azonenberg/latentred/rtl/engine/fabric/LineCardFIFOReader.sv

`timescale 1ns / 1ps
`default_nettype none
/***********************************************************************************************************************
*                                                                                                                      *
* LATENTRED                                                                                                            *
*                                                                                                                      *
* Copyright (c) 2012-2025 Andrew D. Zonenberg                                                                          *
* All rights reserved.                                                                                                 *
*                                                                                                                      *
* Redistribution and use in source and binary forms, with or without modification, are permitted provided that the     *
* following conditions are met:                                                                                        *
*                                                                                                                      *
*    * Redistributions of source code must retain the above copyright notice, this list of conditions, and the         *
*      following disclaimer.                                                                                           *
*                                                                                                                      *
*    * Redistributions in binary form must reproduce the above copyright notice, this list of conditions and the       *
*      following disclaimer in the documentation and/or other materials provided with the distribution.                *
*                                                                                                                      *
*    * Neither the name of the author nor the names of any contributors may be used to endorse or promote products     *
*      derived from this software without specific prior written permission.                                           *
*                                                                                                                      *
* THIS SOFTWARE IS PROVIDED BY THE AUTHORS "AS IS" AND ANY EXPRESS OR IMPLIED WARRANTIES, INCLUDING, BUT NOT LIMITED   *
* TO, THE IMPLIED WARRANTIES OF MERCHANTABILITY AND FITNESS FOR A PARTICULAR PURPOSE ARE DISCLAIMED. IN NO EVENT SHALL *
* THE AUTHORS BE HELD LIABLE FOR ANY DIRECT, INDIRECT, INCIDENTAL, SPECIAL, EXEMPLARY, OR CONSEQUENTIAL DAMAGES        *
* (INCLUDING, BUT NOT LIMITED TO, PROCUREMENT OF SUBSTITUTE GOODS OR SERVICES; LOSS OF USE, DATA, OR PROFITS; OR       *
* BUSINESS INTERRUPTION) HOWEVER CAUSED AND ON ANY THEORY OF LIABILITY, WHETHER IN CONTRACT, STRICT LIABILITY, OR TORT *
* (INCLUDING NEGLIGENCE OR OTHERWISE) ARISING IN ANY WAY OUT OF THE USE OF THIS SOFTWARE, EVEN IF ADVISED OF THE       *
* POSSIBILITY OF SUCH DAMAGE.                                                                                          *
*                                                                                                                      *
***********************************************************************************************************************/

/**
	@file
	@author Andrew D. Zonenberg
	@brief Read-side logic for the RX FIFO
 */

module LineCardFIFOReader #(

	//Global index of the first port in our line card
	parameter BASE_PORT			= 0,

	//Index of the crossbar port we're attached to
	parameter XBAR_PORT			= 0,

	parameter NUM_PORTS			= 50,
	localparam PORT_BITS		= $clog2(NUM_PORTS)

) (
	input wire					clk,

	//Read FIFO state
	input wire[12:0]			wr_ptr_committed[23:0],
	input wire					rd_ptr_reset[23:0],
	output logic[12:0]			rd_ptr[23:0],

	//URAM interface
	output logic				rd_en	= 0,
	output logic[16:0]			rd_addr	= 0,
	input wire[71:0]			rd_data,
	input wire					rd_valid,

	//Request/lookup interface to MAC address table
	AXIStream.transmitter		axi_lookup,
	AXIStream.receiver			axi_results,

	//AXI interface to core crossbar
	AXIStream.transmitter		axi_tx,
	input wire					xbar_ready
);

	////////////////////////////////////////////////////////////////////////////////////////////////////////////////////
	// Validate buses are the right size

	if(axi_tx.DATA_WIDTH != 64)
		axi_bus_width_inconsistent();

	////////////////////////////////////////////////////////////////////////////////////////////////////////////////////
	// Hook up AXI control signals

	assign axi_tx.aclk			= clk;
	assign axi_tx.twakeup		= 1;

	assign axi_lookup.aclk		= clk;
	assign axi_lookup.twakeup	= 1;

	assign axi_results.tready	= 1;

	initial begin
		axi_tx.areset_n		= 0;
		axi_tx.tvalid		= 0;
		axi_tx.tdata		= 0;
		axi_tx.tkeep		= 0;
		axi_tx.tstrb		= 0;
		axi_tx.tdest		= 0;
		axi_tx.tuser		= 0;
		axi_tx.tlast		= 0;

		axi_lookup.areset_n	= 0;
		axi_lookup.tvalid	= 0;
		axi_lookup.tdata	= 0;
		axi_lookup.tkeep	= 0;
		axi_lookup.tstrb	= 0;
		axi_lookup.tdest	= 0;
		axi_lookup.tuser	= 0;
		axi_lookup.tlast	= 0;
		axi_lookup.tid		= 0;
	end

	always_ff @(posedge clk) begin
		axi_tx.areset_n		<= 1;
		axi_lookup.areset_n	<= 1;
	end

	////////////////////////////////////////////////////////////////////////////////////////////////////////////////////
	// Stuff used to index state tables

	typedef enum logic[2:0]
	{
		//0 reserved for now
		MTYPE_HEADER	= 1,	//header read
		MTYPE_WORD0		= 2,
		MTYPE_WORD1		= 3,
		MTYPE_BODY		= 4,
		MTYPE_PREFETCH	= 5
	} mtype_t;

	//Round robin port counter
	logic[4:0]	main_rr_port	= 0;

	typedef struct packed
	{
		mtype_t		mtype;
		logic[4:0]	port;
	} PendingMetadata;

	PendingMetadata	meta_rdata;

	//Source of the packet currently being forwarded
	logic[4:0]		fwd_port	= 0;

	////////////////////////////////////////////////////////////////////////////////////////////////////////////////////
	// Per-port state tables

	typedef enum logic[3:0]
	{
		PORT_STATE_IDLE					= 0,	//nothing to do
		PORT_STATE_DATA_READY			= 1,	//frame ready to start forwarding
		PORT_STATE_HEADER				= 2,	//read of header was dispatched
		PORT_STATE_WORD_0				= 3,	//read of first payload word was dispatched
		PORT_STATE_WORD_1				= 4,	//read of second payload word was dispatched
		PORT_STATE_PREFETCH				= 5,	//prefetching more of the packet
		PORT_STATE_MAC_LOOKUP			= 6,	//mac address lookup in progress
		PORT_STATE_FWD_READY			= 7,	//ready to forward
		PORT_STATE_FORWARDING			= 8		//actively forwarding
	} PortState;

	//Current forwarding state
	PortState				port_states[23:0];

	//VLAN of the current frame
	vlan_t					port_vlans_replica0[23:0];
	vlan_t					port_vlans_replica1[23:0];

	//Dest MAC of the current frame
	macaddr_t				port_dst_mac_replica0[23:0];
	macaddr_t				port_dst_mac_replica1[23:0];

	//Source MAC of the current frame
	logic[15:0]				port_src_mac_hi_replica0[23:0];
	logic[15:0]				port_src_mac_hi_replica1[23:0];
	logic[31:0]				port_src_mac_lo_replica0[23:0];
	//logic[31:0]				port_src_mac_lo_replica1[23:0];

	//First 4 payload bytes of the current frame (ethertype and two more after)
	logic[31:0]				port_first4[23:0];

	//Length of the current frame
	logic[10:0]				port_lens[23:0];

	//Destination port of the current frame
	logic[PORT_BITS-1:0]	port_dst_port[23:0];
	logic					port_dst_is_broadcast[23:0];

	initial begin
		for(integer i=0; i<24; i++) begin
			port_states[i]				= PORT_STATE_IDLE;
			port_vlans_replica0[i]		= 0;
			port_vlans_replica1[i]		= 0;
			port_lens[i]				= 0;
			port_dst_mac_replica0[i]	= 0;
			port_dst_mac_replica1[i]	= 0;
			port_src_mac_hi_replica0[i]	= 0;
			port_src_mac_hi_replica1[i]	= 0;
			port_src_mac_lo_replica0[i]	= 0;
			//port_src_mac_lo_replica1[i]	= 0;
			port_first4[i]				= 0;
			port_dst_port[i]			= 0;
			port_dst_is_broadcast[i]	= 0;
			rd_ptr[i]					= 0;
		end
	end

	//Read side
	macaddr_t				port_dst_mac_metaport;
	macaddr_t				port_dst_mac_mainport;
	vlan_t					port_vlan_metaport;
	vlan_t					port_vlan_mainport;
	logic[10:0]				port_len_rdata;
	logic[15:0]				port_src_mac_hi_metaport;
	logic[15:0]				port_src_mac_hi_rrport;
	logic[31:0]				port_src_mac_lo_fwdport;
	always_comb begin
		port_dst_mac_metaport 		= port_dst_mac_replica0[meta_rdata.port];
		port_dst_mac_mainport 		= port_dst_mac_replica1[main_rr_port];

		port_vlan_metaport 			= port_vlans_replica0[meta_rdata.port];
		port_vlan_mainport 			= port_vlans_replica1[main_rr_port];

		port_len_rdata				= port_lens[main_rr_port];

		port_src_mac_hi_metaport	= port_src_mac_hi_replica0[meta_rdata.port];
		port_src_mac_lo_fwdport		= port_src_mac_lo_replica0[fwd_port];
		port_src_mac_hi_rrport		= port_src_mac_hi_replica1[main_rr_port];
	end

	//Write side
	logic		port_dst_mac_we;
	logic		port_vlan_we;
	logic		port_len_we;
	logic		port_src_mac_hi_we;
	logic		port_src_mac_lo_we;

	macaddr_t	port_dst_mac_wdata;
	vlan_t		port_vlan_wdata;
	logic[10:0]	port_len_wdata;
	logic[15:0]	port_src_mac_hi_wdata;
	logic[31:0]	port_src_mac_lo_wdata;

	always_comb begin
		port_vlan_we		= rd_valid && (meta_rdata.mtype == MTYPE_HEADER);
		port_len_we			= rd_valid && (meta_rdata.mtype == MTYPE_HEADER);
		port_dst_mac_we		= rd_valid && (meta_rdata.mtype == MTYPE_WORD0);
		port_src_mac_hi_we	= rd_valid && (meta_rdata.mtype == MTYPE_WORD0);
		port_src_mac_lo_we	= rd_valid && (meta_rdata.mtype == MTYPE_WORD1);

		port_dst_mac_wdata	=
		{
			rd_data[0*8 +: 8],
			rd_data[1*8 +: 8],
			rd_data[2*8 +: 8],
			rd_data[3*8 +: 8],
			rd_data[4*8 +: 8],
			rd_data[5*8 +: 8]
		};

		port_src_mac_hi_wdata =
		{
			rd_data[6*8 +: 8],
			rd_data[7*8 +: 8]
		};

		port_src_mac_lo_wdata =
		{
			rd_data[0*8 +: 8],
			rd_data[1*8 +: 8],
			rd_data[2*8 +: 8],
			rd_data[3*8 +: 8]
		};

		port_vlan_wdata		= rd_data[27:16];
		port_len_wdata		= rd_data[10:0];
	end
	always_ff @(posedge clk) begin
		if(port_dst_mac_we) begin
			port_dst_mac_replica0[meta_rdata.port]		<= port_dst_mac_wdata;
			port_dst_mac_replica1[meta_rdata.port]		<= port_dst_mac_wdata;
		end

		if(port_vlan_we) begin
			port_vlans_replica0[meta_rdata.port]		<= port_vlan_wdata;
			port_vlans_replica1[meta_rdata.port]		<= port_vlan_wdata;
		end

		if(port_len_we)
			port_lens[meta_rdata.port]					<= port_len_wdata;

		if(port_src_mac_hi_we) begin
			port_src_mac_hi_replica0[meta_rdata.port]	<= port_src_mac_hi_wdata;
			port_src_mac_hi_replica1[meta_rdata.port]	<= port_src_mac_hi_wdata;
		end

		if(port_src_mac_lo_we) begin
			port_src_mac_lo_replica0[meta_rdata.port]	<= port_src_mac_lo_wdata;
			//port_src_mac_lo_replica1[meta_rdata.port]	<= port_src_mac_lo_wdata;
		end

	end

	////////////////////////////////////////////////////////////////////////////////////////////////////////////////////
	// FIFO read helpers

	logic[12:0] fifo_rd_size[23:0];
	always_comb begin
		for(integer i=0; i<24; i=i+1)
			fifo_rd_size[i] = wr_ptr_committed[i] - rd_ptr[i];
	end

	////////////////////////////////////////////////////////////////////////////////////////////////////////////////////
	// State for in-progress packets

	PendingMetadata meta_wdata;

	wire			meta_empty;

	SingleClockFifo #(
		.WIDTH($bits(PendingMetadata)),
		.DEPTH(32),
		.USE_BLOCK(0),
		.OUT_REG(0)
	) meta_fifo (
		.clk(clk),

		.wr(rd_en),
		.din(meta_wdata),

		.rd(rd_valid),
		.dout(meta_rdata),

		.overflow(),
		.underflow(),
		.empty(meta_empty),
		.full(),
		.rsize(),
		.wsize(),
		.reset(!axi_tx.areset_n)
	);

	always_comb begin
		meta_wdata.port	= rd_addr[16:12];
	end

	////////////////////////////////////////////////////////////////////////////////////////////////////////////////////
	// Prefetch buffer

	//The actual memory
	logic[63:0] prefetch_buf[255:0];

	initial begin
		for(integer i=0; i<256; i++)
			prefetch_buf[i]	= 0;
	end

	//Prefetch progress for the current frame
	logic[2:0]		prefetch_wr_count		= 0;
	logic[2:0]		prefetch_wr_count_ff	= 0;
	logic[2:0]		prefetch_wr_count_ff2	= 0;
	logic[2:0]		prefetch_wr_count_ff3	= 0;
	logic[2:0]		prefetch_wr_count_ff4	= 0;
	logic[2:0]		prefetch_wr_count_ff5	= 0;
	logic[2:0]		prefetch_wr_count_ff6	= 0;

	logic			prefetch_wr_en;
	logic[7:0]		prefetch_wr_addr;
	logic[7:0]		prefetch_rd_addr		= 0;
	logic[63:0]		prefetch_rd_data;
	always_comb begin
		prefetch_wr_en		= rd_valid && (meta_rdata.mtype == MTYPE_PREFETCH);
		prefetch_wr_addr	= { meta_rdata.port, prefetch_wr_count_ff6 };
		prefetch_rd_data	= prefetch_buf[prefetch_rd_addr];
	end

	//Writes
	always_ff @(posedge clk) begin
		prefetch_wr_count_ff	<= prefetch_wr_count;
		prefetch_wr_count_ff2	<= prefetch_wr_count_ff;
		prefetch_wr_count_ff3	<= prefetch_wr_count_ff2;
		prefetch_wr_count_ff4	<= prefetch_wr_count_ff3;
		prefetch_wr_count_ff5	<= prefetch_wr_count_ff4;
		prefetch_wr_count_ff6	<= prefetch_wr_count_ff5;

		if(prefetch_wr_en)
			prefetch_buf[prefetch_wr_addr]	<= rd_data[63:0];
	end

	//Reads

	////////////////////////////////////////////////////////////////////////////////////////////////////////////////////
	// Main reader block

	//FIFO read pointer of the round robin winner
	logic[11:0]	main_rr_ptr;

	//FIFO read pointer of the most recent read transaction
	logic[11:0] meta_rdata_ptr;

	//FIFO read pointer of the frame being forwarded
	logic[11:0] fwd_ptr;

	always_comb begin
		main_rr_ptr		= rd_ptr[main_rr_port][11:0];
		meta_rdata_ptr	= rd_ptr[meta_rdata.port][11:0];
		fwd_ptr			= rd_ptr[fwd_port][11:0];
	end

	logic[10:0]	fwd_bytesToRead	= 0;
	logic[10:0]	fwd_bytesToSend	= 0;

	enum logic[2:0]
	{
		FWD_STATE_IDLE				= 0,
		FWD_STATE_HEADER_1			= 1,
		FWD_STATE_PREFETCH_DATA		= 2,
		FWD_STATE_BODY				= 3,
		FWD_STATE_TAIL				= 4
	} fwd_state = FWD_STATE_IDLE;

	//Figure out if we are available to begin forwarding a frame this cycle
	logic			canStartForwarding;
	always_comb begin

		canStartForwarding = 0;

		//Only proceed if previous frame isn't being actively forwarded
		if(fwd_state == FWD_STATE_IDLE)
			canStartForwarding = xbar_ready;

		//or it's ending this cycle
		if( (fwd_state == FWD_STATE_TAIL) && (fwd_bytesToSend <= 8) )
			canStartForwarding = xbar_ready;

	end

	//Combinatorially decide to increment read pointer
	logic[12:0]		rd_ptr_next[23:0];
	logic			rd_ptr_inc[23:0];
	always_comb begin

		//Default to not incrementing read pointer
		for(integer i=0; i<24; i++)
			rd_ptr_inc[i] = 0;

		//Actively forwarding?
		if( (fwd_state != FWD_STATE_IDLE) && (fwd_state != FWD_STATE_TAIL) ) begin

			case(fwd_state)
				FWD_STATE_HEADER_1:			rd_ptr_inc[fwd_port]	= 1;
				FWD_STATE_PREFETCH_DATA:	rd_ptr_inc[fwd_port]	= (fwd_bytesToRead > 0);
				FWD_STATE_BODY:				rd_ptr_inc[fwd_port]	= (fwd_bytesToRead > 0);
				default: begin
				end
			endcase

		end

		//Main port state machine
		else begin
			case(port_states[main_rr_port])
				PORT_STATE_DATA_READY:	rd_ptr_inc[main_rr_port]	= 1;
				PORT_STATE_HEADER:		rd_ptr_inc[main_rr_port]	= 1;
				PORT_STATE_WORD_0:		rd_ptr_inc[main_rr_port]	= 1;
				PORT_STATE_WORD_1:		rd_ptr_inc[main_rr_port]	= 1;
				PORT_STATE_FWD_READY: begin
					if( (port_len_rdata > 64) && canStartForwarding )
						rd_ptr_inc[main_rr_port]	= 1;
				end
				PORT_STATE_PREFETCH: begin
					if(prefetch_wr_count < 4)
						rd_ptr_inc[main_rr_port]	= 1;
				end

			endcase
		end

		//Calculate new read pointers
		for(integer i=0; i<24; i++) begin

			//Reset read pointer on request
			if(rd_ptr_reset[i])
				rd_ptr_next[i]		= 0;
			else if(rd_ptr_inc[i])
				rd_ptr_next[i]		= rd_ptr[i] + 1;
			else
				rd_ptr_next[i]		= rd_ptr[i];
		end

	end

	always_ff @(posedge clk) begin

		rd_en					<= 0;
		axi_lookup.tvalid		<= 0;
		axi_lookup.tlast		<= 0;

		//Clear AXI stuff on ack
		if(axi_tx.tready) begin
			axi_tx.tvalid		<= 0;
			axi_tx.tkeep		<= 0;
			axi_tx.tstrb		<= 0;
			axi_tx.tdata		<= 0;
			axi_tx.tlast		<= 0;
		end

		for(integer i=0; i<24; i++) begin

			//Register the calculated read pointer values
			//TODO: explicit replication for fanout control?
			rd_ptr[i]		<= rd_ptr_next[i];

			//Check all ports in parallel for having data ready to go
			if( (port_states[i] == PORT_STATE_IDLE) && (fifo_rd_size[i] != 0) )
				port_states[i]	<= PORT_STATE_DATA_READY;
		end

		//Handle MAC address lookups coming back
		if(axi_results.tvalid) begin
			port_dst_is_broadcast[axi_results.tid]	<= !axi_results.tuser[0];
			port_dst_port[axi_results.tid]			<= axi_results.tdata;
			port_states[axi_results.tid]			<= PORT_STATE_FWD_READY;

			`ifdef SIMULATION
				$display("[%t] Frame on interface %d is ready to forward",
					$realtime(),
					axi_results.tid + BASE_PORT);
			`endif
		end

		//Forwarding payload body
		if( (fwd_state == FWD_STATE_TAIL) || (fwd_state == FWD_STATE_BODY) ) begin

			//Full word?
			if(fwd_bytesToSend > 8) begin
				fwd_bytesToSend				<= fwd_bytesToSend - 8;
				axi_tx.tstrb				<= 8'hff;
			end

			//Partial word? We're done
			else begin
				case(fwd_bytesToSend)
					7:	axi_tx.tstrb		<= 8'b01111111;
					6:	axi_tx.tstrb		<= 8'b00111111;
					5:	axi_tx.tstrb		<= 8'b00011111;
					4:	axi_tx.tstrb		<= 8'b00001111;
					3:	axi_tx.tstrb		<= 8'b00000111;
					2:	axi_tx.tstrb		<= 8'b00000011;
					1:	axi_tx.tstrb		<= 8'b00000001;
					default: begin
						axi_tx.tstrb		<= 8'b00000000;
					end
				endcase

				axi_tx.tlast				<= 1;
				fwd_bytesToSend				<= 0;

				//Clear lots of state
				fwd_state					<= FWD_STATE_IDLE;
				port_states[fwd_port]		<= PORT_STATE_IDLE;

			end

			axi_tx.tvalid					<= 1;
			axi_tx.tdata					<= rd_data[63:0];
			axi_tx.tkeep					<= 8'hff;

		end

		//Request more data if we're fetching the body from URAM
		if(fwd_state == FWD_STATE_BODY) begin

			//Request more data unless we're done
			if(fwd_bytesToRead > 0) begin

				if(fwd_bytesToRead >= 8)
					fwd_bytesToRead				<= fwd_bytesToRead - 8;
				else
					fwd_bytesToRead				<= 0;

				//Request a read of the data
				rd_en							<= 1;
				rd_addr							<= { fwd_port, fwd_ptr };
				meta_wdata.mtype				<= MTYPE_BODY;

			end

			//Done reading? Move to tail unless this was a min-sized frame with no tail needed after prefetch
			else if(fwd_bytesToSend > 8)
				fwd_state						<= FWD_STATE_TAIL;

		end

		//Prefetch data while waiting for MAC lookup
		if(fwd_state == FWD_STATE_PREFETCH_DATA) begin

			//Advance
			prefetch_rd_addr			<= prefetch_rd_addr + 1;
			fwd_bytesToSend				<= fwd_bytesToSend - 8;

			//Send data
			axi_tx.tvalid				<= 1;
			axi_tx.tdata				<= prefetch_rd_data;
			axi_tx.tkeep				<= 8'hff;
			axi_tx.tstrb				<= 8'hff;

			//Once we get to the end of the prefetch, time to move on to normal forwarding
			if(prefetch_rd_addr[2:0] == 4)
				fwd_state				<= FWD_STATE_BODY;

			//Cannot end a frame here, prefetch depth isn't long enough
			//So no check for fwd_bytesToSend being too small

			//Request more data unless we're done
			if(fwd_bytesToRead > 0) begin

				if(fwd_bytesToRead >= 8)
					fwd_bytesToRead				<= fwd_bytesToRead - 8;
				else
					fwd_bytesToRead				<= 0;

				//Request a read of the data
				rd_en							<= 1;
				rd_addr							<= { fwd_port, fwd_ptr };
				meta_wdata.mtype				<= MTYPE_BODY;

			end

		end

		//Read data will always show up after the metadata, so no need to check if there's data in the metadata fifo
		if(rd_valid) begin

			//Figure out why we read it
			case(meta_rdata.mtype)

				//nothing to do, handled in memory write block
				MTYPE_HEADER: begin
				end //MTYPE_HEADER

				MTYPE_WORD0: begin
				end //MTYPE_WORD0

				//Second packet word
				MTYPE_WORD1: begin

					//Save the remaining headers
					port_first4[meta_rdata.port]		<=
					{
						rd_data[4*8 +: 8],
						rd_data[5*8 +: 8],
						rd_data[6*8 +: 8],
						rd_data[7*8 +: 8]
					};

					//Don't dispatch a new memory request
					//Just mark the state as ready to go for routing lookup
					port_states[meta_rdata.port]		<= PORT_STATE_MAC_LOOKUP;

					//Dispatch the MAC address lookup
					axi_lookup.tvalid					<= 1;
					axi_lookup.tlast					<= 1;
					axi_lookup.tdata					<=
					{
						meta_rdata.port + BASE_PORT,
						port_vlan_metaport,

						//src mac comes in two chunks
						port_src_mac_hi_metaport,
						port_src_mac_lo_wdata,

						port_dst_mac_metaport
					};
					axi_lookup.tid						<= meta_rdata.port;
					axi_lookup.tdest					<= XBAR_PORT;

				end	//MTYPE_WORD1

				//Don't know why? Ignore the read
				default: begin
				end
			endcase

		end

		//Handle forwarding paths that can trigger memory reads
		if( (fwd_state != FWD_STATE_IDLE) && (fwd_state != FWD_STATE_TAIL) ) begin

			if(fwd_state == FWD_STATE_HEADER_1) begin

				//Request a read of the data
				if(fwd_bytesToRead > 0) begin
					rd_en						<= 1;
					rd_addr						<= { fwd_port, fwd_ptr };
					meta_wdata.mtype			<= MTYPE_BODY;

					if(fwd_bytesToRead > 8)
						fwd_bytesToRead			<= fwd_bytesToRead - 8;
					else
						fwd_bytesToRead			<= 0;

				end

				fwd_bytesToSend					<= fwd_bytesToSend - 8;
				axi_tx.tvalid					<= 1;
				axi_tx.tdata					<=
				{
					port_first4[fwd_port][0*8 +: 8],
					port_first4[fwd_port][1*8 +: 8],
					port_first4[fwd_port][2*8 +: 8],
					port_first4[fwd_port][3*8 +: 8],
					port_src_mac_lo_fwdport[0*8 +: 8],
					port_src_mac_lo_fwdport[1*8 +: 8],
					port_src_mac_lo_fwdport[2*8 +: 8],
					port_src_mac_lo_fwdport[3*8 +: 8]
				};
				axi_tx.tstrb					<= 8'hff;
				axi_tx.tkeep					<= 8'hff;

				fwd_state						<= FWD_STATE_PREFETCH_DATA;
				prefetch_rd_addr				<= { fwd_port, 3'h0 };
			end

			//other states need to block main state machine from sending memory requests but need not do anything here

		end

		//No action needed based on a previously read word.
		//Start processing new stuff, if we have something to do.
		else begin

			//Default to bumping round robin counter
			main_rr_port						<= main_rr_port + 1;
			if(main_rr_port == 23)
				main_rr_port					<= 0;

			//See what the current port state is and if any action is needed
			case(port_states[main_rr_port])

				//New frame ready to forward
				PORT_STATE_DATA_READY: begin

					`ifdef SIMULATION
						$display("[%t] Frame arrived on interface %d, starting lookup process",
							$realtime(),
							main_rr_port + BASE_PORT);
					`endif

					//Request a read of the header
					rd_en								<= 1;
					rd_addr								<= { main_rr_port, main_rr_ptr };
					meta_wdata.mtype					<= MTYPE_HEADER;
					port_states[main_rr_port]			<= PORT_STATE_HEADER;

					//Do not bump the RR pointer, we want to read the next word next clock
					main_rr_port						<= main_rr_port;

				end	//PORT_STATE_DATA_READY

				//Header read in progress
				PORT_STATE_HEADER: begin

					//Request read of the first frame word
					rd_en							<= 1;
					rd_addr							<= { main_rr_port, main_rr_ptr };
					meta_wdata.mtype				<= MTYPE_WORD0;
					port_states[main_rr_port]		<= PORT_STATE_WORD_0;

					//Do not bump the RR pointer, we want to read the next word next clock
					main_rr_port					<= main_rr_port;

				end //PORT_STATE_HEADER

				//First data word in progress
				PORT_STATE_WORD_0: begin

					//Request read of the second frame word
					rd_en							<= 1;
					rd_addr							<= { main_rr_port, main_rr_ptr };
					meta_wdata.mtype				<= MTYPE_WORD1;

					port_states[main_rr_port]		<= PORT_STATE_WORD_1;

					//Do not bump the RR pointer, we want to read the next word next clock
					main_rr_port					<= main_rr_port;

				end	//PORT_STATE_WORD_0

				//Second data word in progress: start prefetching
				PORT_STATE_WORD_1: begin

					prefetch_wr_count				<= 0;

					//Prefetch
					rd_en							<= 1;
					rd_addr							<= { main_rr_port, main_rr_ptr };
					meta_wdata.mtype				<= MTYPE_PREFETCH;

					port_states[main_rr_port]		<= PORT_STATE_PREFETCH;

					//Do not bump the RR pointer, we want to read the next word next clock
					main_rr_port					<= main_rr_port;

				end	//PORT_STATE_WORD_1

				PORT_STATE_PREFETCH: begin

					//Done?
					if(prefetch_wr_count < 4) begin

						prefetch_wr_count			<= prefetch_wr_count + 1;

						//Read the data
						rd_en						<= 1;
						rd_addr						<= { main_rr_port, main_rr_ptr };
						meta_wdata.mtype			<= MTYPE_PREFETCH;

						//Do not bump the RR pointer, we want to read the next word next clock
						main_rr_port				<= main_rr_port;

					end

				end //PORT_STATE_PREFETCH

				PORT_STATE_FWD_READY: begin

					if(canStartForwarding) begin

						`ifdef SIMULATION
							$display("[%t] Starting forward of frame from interface %d",
								$realtime(),
								main_rr_port + BASE_PORT);
						`endif

						//Request a read of the data (56 bytes read previously by header/prefetch, 8 this cycle)
						//Ethernet minimum frame size is 64 bytes so we'll always need to read this much
						rd_en							<= 1;
						rd_addr							<= { main_rr_port, main_rr_ptr };
						meta_wdata.mtype				<= MTYPE_BODY;
						if(port_len_rdata > 64)
							fwd_bytesToRead				<= port_len_rdata - 64;
						else
							fwd_bytesToRead				<= 0;

						//We've started to forward the frame, 8 bytes forwarded so far
						fwd_state						<= FWD_STATE_HEADER_1;
						fwd_bytesToSend					<= port_len_rdata - 8;
						port_states[main_rr_port]		<= PORT_STATE_FORWARDING;

						//Save the port number
						fwd_port						<= main_rr_port;

						//Start sending previously-read data out the AXI bus
						axi_tx.tvalid					<= 1;
						axi_tx.tdata					<=
						{
							port_src_mac_hi_rrport[0*8 +: 8],
							port_src_mac_hi_rrport[1*8 +: 8],
							port_dst_mac_mainport[0*8 +: 8],
							port_dst_mac_mainport[1*8 +: 8],
							port_dst_mac_mainport[2*8 +: 8],
							port_dst_mac_mainport[3*8 +: 8],
							port_dst_mac_mainport[4*8 +: 8],
							port_dst_mac_mainport[5*8 +: 8]
						};
						axi_tx.tstrb					<= 8'hff;
						axi_tx.tkeep					<= 8'hff;
						axi_tx.tuser					<= port_vlan_mainport;
						axi_tx.tdest					<=
						{
							port_dst_is_broadcast[main_rr_port],
							port_dst_port[main_rr_port]
						};
					end

				end

				default: begin
				end

			endcase

		end

	end

endmodule
