azonenberg/latentred/firmware/lcbringup/staticnet-config.h

/***********************************************************************************************************************
*                                                                                                                      *
* LATENTRED                                                                                                            *
*                                                                                                                      *
* Copyright (c) 2023-2025 Andrew D. Zonenberg and contributors                                                         *
* All rights reserved.                                                                                                 *
*                                                                                                                      *
* Redistribution and use in source and binary forms, with or without modification, are permitted provided that the     *
* following conditions are met:                                                                                        *
*                                                                                                                      *
*    * Redistributions of source code must retain the above copyright notice, this list of conditions, and the         *
*      following disclaimer.                                                                                           *
*                                                                                                                      *
*    * Redistributions in binary form must reproduce the above copyright notice, this list of conditions and the       *
*      following disclaimer in the documentation and/or other materials provided with the distribution.                *
*                                                                                                                      *
*    * Neither the name of the author nor the names of any contributors may be used to endorse or promote products     *
*      derived from this software without specific prior written permission.                                           *
*                                                                                                                      *
* THIS SOFTWARE IS PROVIDED BY THE AUTHORS "AS IS" AND ANY EXPRESS OR IMPLIED WARRANTIES, INCLUDING, BUT NOT LIMITED   *
* TO, THE IMPLIED WARRANTIES OF MERCHANTABILITY AND FITNESS FOR A PARTICULAR PURPOSE ARE DISCLAIMED. IN NO EVENT SHALL *
* THE AUTHORS BE HELD LIABLE FOR ANY DIRECT, INDIRECT, INCIDENTAL, SPECIAL, EXEMPLARY, OR CONSEQUENTIAL DAMAGES        *
* (INCLUDING, BUT NOT LIMITED TO, PROCUREMENT OF SUBSTITUTE GOODS OR SERVICES; LOSS OF USE, DATA, OR PROFITS; OR       *
* BUSINESS INTERRUPTION) HOWEVER CAUSED AND ON ANY THEORY OF LIABILITY, WHETHER IN CONTRACT, STRICT LIABILITY, OR TORT *
* (INCLUDING NEGLIGENCE OR OTHERWISE) ARISING IN ANY WAY OUT OF THE USE OF THIS SOFTWARE, EVEN IF ADVISED OF THE       *
* POSSIBILITY OF SUCH DAMAGE.                                                                                          *
*                                                                                                                      *
***********************************************************************************************************************/

/**
	@file
	@brief Configuration file for staticnet on LATENTRED
 */

#ifndef staticnet_config_h
#define staticnet_config_h

///@brief Maximum size of an Ethernet frame (payload only, headers not included)
#define ETHERNET_PAYLOAD_MTU 1500

///@brief Define this to zeroize all frame buffers between uses
//#define ZEROIZE_BUFFERS_BEFORE_USE

///@brief Define this to enable performance counters
#define STATICNET_PERFORMANCE_COUNTERS

///@brief Number of ways of associativity for the ARP cache
#define ARP_CACHE_WAYS 4

///@brief Number of lines per set in the ARP cache
#define ARP_CACHE_LINES 256

///@brief Number of entries in the TCP socket table
#define TCP_TABLE_WAYS 2

///@brief Number of lines per set in the TCP socket table
#define TCP_TABLE_LINES 16

///@brief Maximum number of SSH connections supported
#define SSH_TABLE_SIZE 2

///@brief SSH socket RX buffer size
#define SSH_RX_BUFFER_SIZE 2048

///@brief CLI TX buffer size
#define CLI_TX_BUFFER_SIZE 1024

///@brief Maximum length of a SSH username
#define SSH_MAX_USERNAME	32

///@brief Max length of a CLI username
#define CLI_USERNAME_MAX SSH_MAX_USERNAME

///@brief Maximum length of a SSH password
#define SSH_MAX_PASSWORD	128

///@brief Max number of concurrent SCPI connections
#define MAX_SCPI_CONNS	2

///@brief SCPI socket RX buffer size
#define SCPI_RX_BUFFER_SIZE 2048

/**
	@brief Number of (1500 byte + metadata) transmit buffers to allocate

	This should be as large as possible to enable lots of outstanding un-ACKed TCP segments
 */
#define APB_TX_BUFCOUNT 24

/**
	@brief Number of (1500 byte + metadata) receive buffers to allocate

	This can be pretty small because of our single threaded event loop, we don't hold onto RX buffers much.
	More importantly, we typically do most of our RX buffering on the FPGA and just pull from that as data shows up.
 */
#define APB_RX_BUFCOUNT 2

/**
	@brief Max number of requests we allow outstanding to a single SFTP endpoint
 */
#define SFTP_MAX_REQUESTS 20

/**
	@brief Max pending (not ACKed) TCP segments for a given socket

	This is essentially a cap on window size in segments (vs bytes).
 */
#define TCP_MAX_UNACKED APB_TX_BUFCOUNT

///@brief Maximum age for a TCP segment before deciding to retransmit (in 100ms ticks)
#define TCP_RETRANSMIT_TIMEOUT 2

///@brief If true, we have hardware offload for UDP checksums and should not waste time calculating them in firmware
//#define HAVE_UDP_V4_CHECKSUM_OFFLOAD

///@brief If true, we have hardware offload for TCP checksums and should not waste time calculating them in firmware
//#define HAVE_TCP_V4_CHECKSUM_OFFLOAD

///@brief If set, we can do 64-bit burst transactions on the FMC to transmit
//#define HAVE_APB64_TX

#endif
