azonenberg/latentred/sims/switch-engine/arc6-launches/arc6-launch-cutout-comparison_data/imgui.ini

[Window][Waveform Group 1]
Pos=253,69
Size=1822,540
Collapsed=0
DockId=0x0000000A,1

[Window][Waveform Group 2]
Pos=253,69
Size=1822,540
Collapsed=0
DockId=0x0000000A,0

[Window][DockSpaceViewport_11111111]
Pos=0,46
Size=2082,1101
Collapsed=0

[Window][Workspace 1]
Pos=246,46
Size=1836,1071
Collapsed=0
DockId=0x00000002,0

[Window][Stream Browser]
Pos=0,46
Size=245,1071
Collapsed=0
DockId=0x00000001,0

[Window][Filter Palette]
Pos=1919,69
Size=156,1041
Collapsed=0
DockId=0x00000004,0

[Window][Filter Graph Editor]
Pos=253,69
Size=1665,1041
Collapsed=0
DockId=0x00000005,0

[Window][FilterGraphErrors]
Pos=0,0
Size=300,400
Collapsed=0
DockId=0x00000006,0

[Window][Debug##Default]
Pos=60,60
Size=400,400
Collapsed=0

[Window][Channel properties: PRBS7(10.3125 Gbps)]
Pos=93,-272
Size=300,400
Collapsed=0

[Window][Channel properties: ]
Pos=93,-272
Size=300,400
Collapsed=0

[Window][Channel properties: DigitaltoNRZ_1]
Pos=60,60
Size=300,400
Collapsed=0

[Window][Waveform Group 3]
Pos=253,610
Size=910,500
Collapsed=0
DockId=0x0000000B,0

[Window][Workspace 24]
Pos=246,46
Size=1836,1071
Collapsed=0
DockId=0x00000002,1

[Window][Measurements]
Pos=60,60
Size=300,400
Collapsed=0

[Window][##MainMenuBar]
Pos=0,0
Size=2082,16
Collapsed=0

[Window][Channel properties: Jitter_1]
Pos=60,60
Size=300,400
Collapsed=0

[Window][Channel properties: Eyepattern_1]
Pos=60,60
Size=300,400
Collapsed=0

[Window][Channel properties: Noise_1]
Pos=60,60
Size=300,400
Collapsed=0

[Window][Waveform Group 4]
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
Pos=326,188
Size=300,400
Collapsed=0

[Window][Waveform Group 5]
Pos=253,69
Size=1822,540
Collapsed=0
DockId=0x0000000A,2

[Window][Cursors (s-params)]
Pos=60,60
Size=540,180
Collapsed=0

[Window][Cursors (Waveform Group 5)]
Pos=60,60
Size=540,180
Collapsed=0

[Window][Waveform Group 6]
Pos=1164,610
Size=911,500
Collapsed=0
DockId=0x0000000C,1

[Window][Channel properties: arc6-frontside7-top1.s2p]
Pos=60,60
Size=300,400
Collapsed=0

[Window][Channel properties: arc6-frontside7-top2.s2p]
Pos=60,60
Size=300,400
Collapsed=0

[Window][Waveform Group 7]
Pos=1164,610
Size=911,500
Collapsed=0
DockId=0x0000000C,1

[Window][Channel properties: arc6-frontside7-top2-bigcut.s2p]
Pos=60,60
Size=300,400
Collapsed=0

[Window][Channel properties: arc6-frontside7-meanderfix-500um-bgacut.s2p]
Pos=1498,157
Size=300,400
Collapsed=0

[Window][Cursors (Waveform Group 1)]
Pos=60,60
Size=540,180
Collapsed=0

[Window][Channel properties: sfp28-tx0-cascade.s2p]
Pos=60,60
Size=300,400
Collapsed=0

[Window][Channel properties: Memory_18]
Pos=60,60
Size=300,400
Collapsed=0

[Window][Channel properties: Memory_19]
Pos=60,60
Size=300,400
Collapsed=0

[Window][Channel properties: sfp28-tx0-part1-differential.s2p]
Pos=60,60
Size=300,400
Collapsed=0

[Window][Channel properties: Memory_20]
ViewportPos=2512,706
ViewportId=0x8DB6F2FE
Size=300,400
Collapsed=0

[Window][Channel properties: Memory_21]
Pos=60,60
Size=300,400
Collapsed=0

[Window][Channel properties: sfp28-tx0-part1-differential-groundl4.s2p]
Pos=60,60
Size=300,400
Collapsed=0

[Window][Channel properties: sfp28-tx0-part4-differential.s2p]
Pos=1102,104
Size=300,400
Collapsed=0

[Table][0xE7B21D1D,2]
RefScale=12
Column 0  Width=144
Column 1  Weight=1.0000

[Table][0xA26D2529,2]
RefScale=12

[Table][0x20DF6973,3]
RefScale=12
Column 0  Width=144
Column 1  Width=16
Column 2  Weight=1.0000

[Table][0x0F698FC7,5]
RefScale=12

[Table][0x5DDED439,2]
RefScale=12

[Table][0xFB57598F,2]
RefScale=12

[Table][0x25989BBC,5]
RefScale=12

[Docking][Data]
DockSpace     ID=0x2E6C0131 Pos=3095,657 Size=1822,1041 Split=X
  DockNode    ID=0x00000003 Parent=0x2E6C0131 SizeRef=629,570 Split=Y
    DockNode  ID=0x00000005 Parent=0x00000003 SizeRef=629,427 CentralNode=1 Selected=0x59483851
    DockNode  ID=0x00000006 Parent=0x00000003 SizeRef=629,142 NoWindowMenuButton=1 NoCloseButton=1 Selected=0xF5AB598A
  DockNode    ID=0x00000004 Parent=0x2E6C0131 SizeRef=156,570 Selected=0x99D07274
DockSpace     ID=0x534583D5 Window=0xD142F969 Pos=3095,657 Size=1822,1041 Split=Y Selected=0x77CAAA94
  DockNode    ID=0x00000007 Parent=0x534583D5 SizeRef=1822,540 Split=Y Selected=0x77CAAA94
    DockNode  ID=0x00000009 Parent=0x00000007 SizeRef=1822,248 Selected=0x3FF91A60
    DockNode  ID=0x0000000A Parent=0x00000007 SizeRef=1822,253 CentralNode=1 Selected=0x3FF91A60
  DockNode    ID=0x00000008 Parent=0x534583D5 SizeRef=1822,500 Split=X Selected=0x07E875CC
    DockNode  ID=0x0000000B Parent=0x00000008 SizeRef=910,500 Selected=0x07E875CC
    DockNode  ID=0x0000000C Parent=0x00000008 SizeRef=911,500 Selected=0xAF9E7B88
DockSpace     ID=0xE48FFB1A Window=0x5F1540D8 Pos=2842,634 Size=2082,1071 Split=X
  DockNode    ID=0x00000001 Parent=0xE48FFB1A SizeRef=245,630 Selected=0x25766ABD
  DockNode    ID=0x00000002 Parent=0xE48FFB1A SizeRef=980,630 CentralNode=1 Selected=0x765077CB
